locnho/chem-feeder-mqtt/test-images/000b.jpg

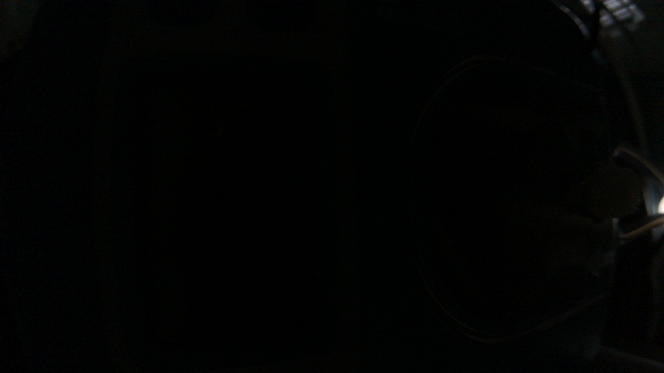
test-images/000b.jpg
