locnho/chem-feeder-mqtt/test-images/000c.jpg

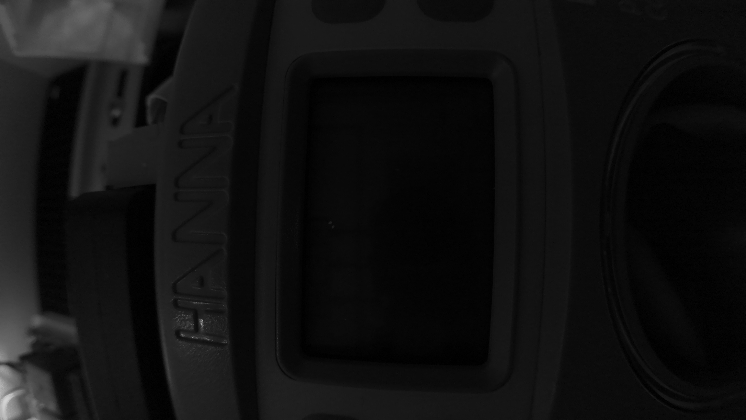
test-images/000c.jpg
