locnho/chem-feeder-mqtt/test-images/680.jpg

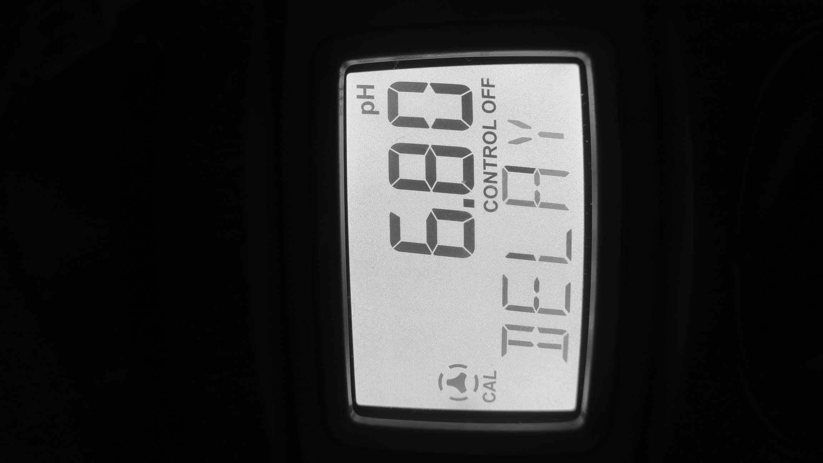
test-images/680.jpg
