locnho/chem-feeder-mqtt/test-images/729.jpg

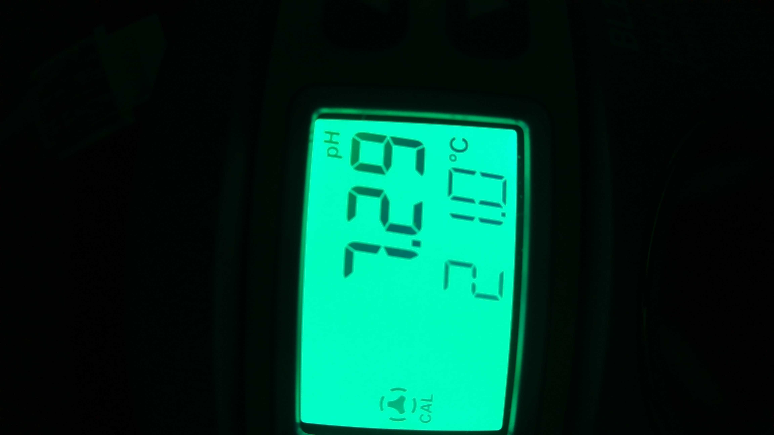
test-images/729.jpg
