locnho/chem-feeder-mqtt/test-images/731.jpg

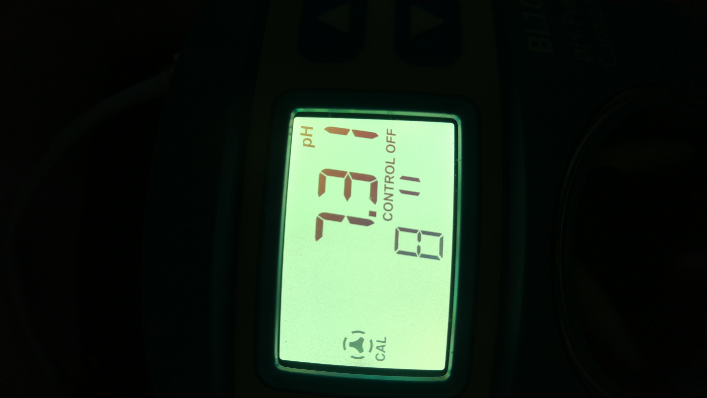
test-images/731.jpg
