locnho/chem-feeder-mqtt/test-images/733.jpg

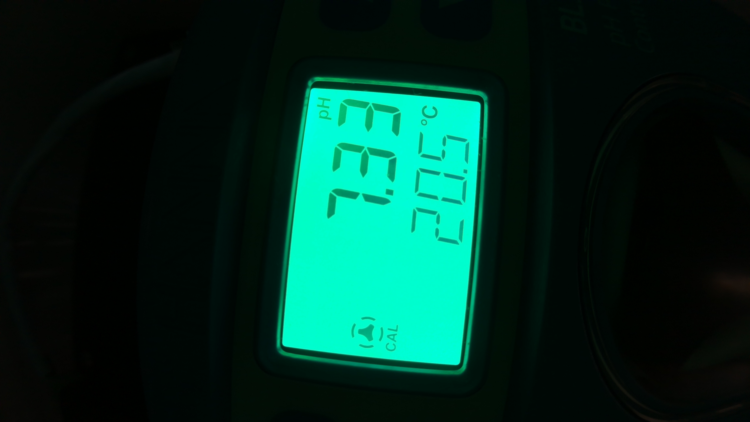
test-images/733.jpg
