locnho/chem-feeder-mqtt/test-images/735b.jpg

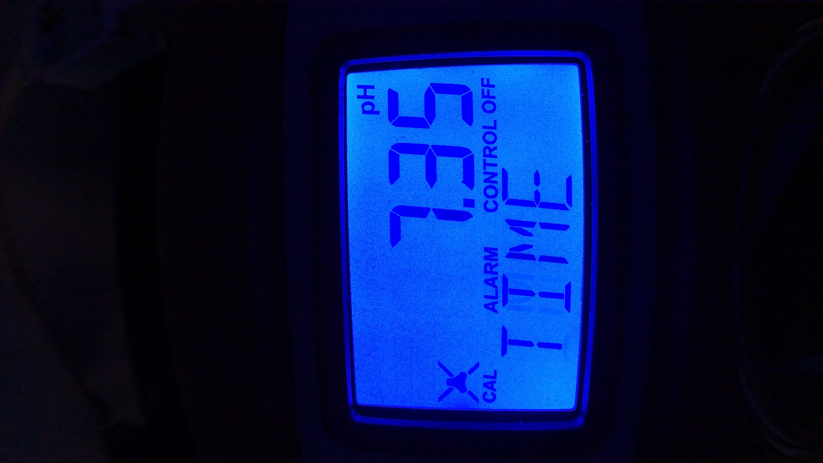
test-images/735b.jpg
