locnho/chem-feeder-mqtt/test-images/740.jpg

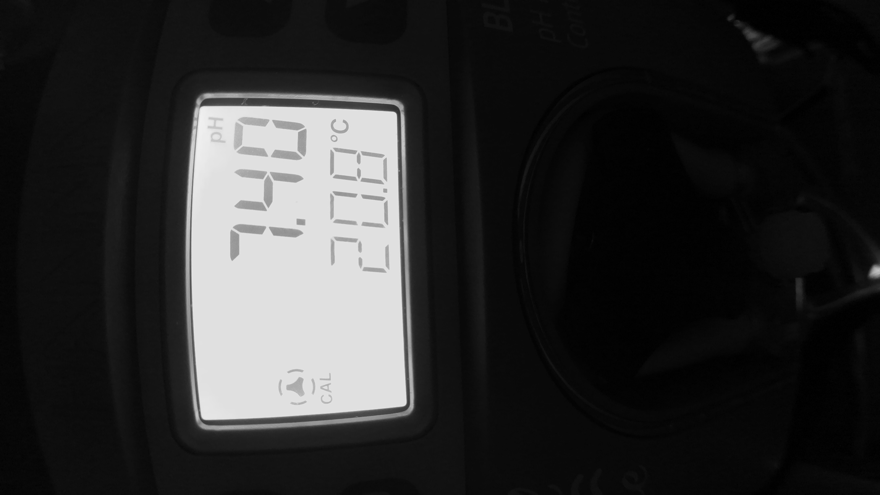
test-images/740.jpg
