locnho/chem-feeder-mqtt/test-images/742a.jpg

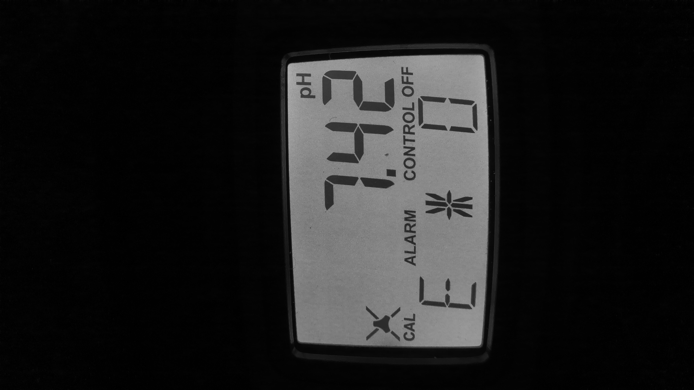
test-images/742a.jpg
