locnho/chem-feeder-mqtt/test-images/742ab.jpg

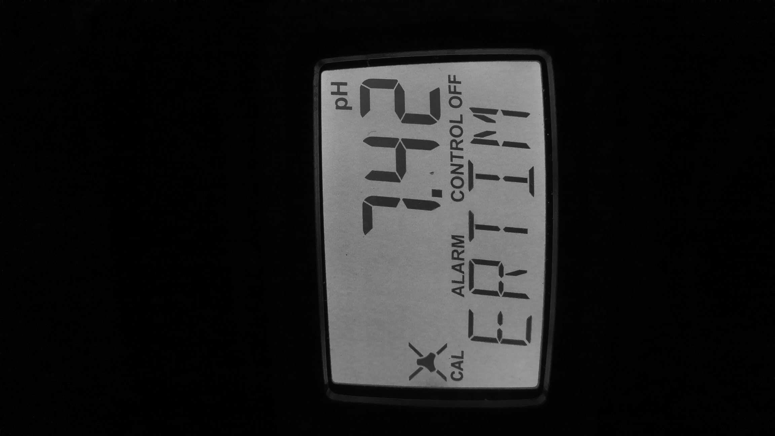
test-images/742ab.jpg
