locnho/chem-feeder-mqtt/test-images/760.jpg

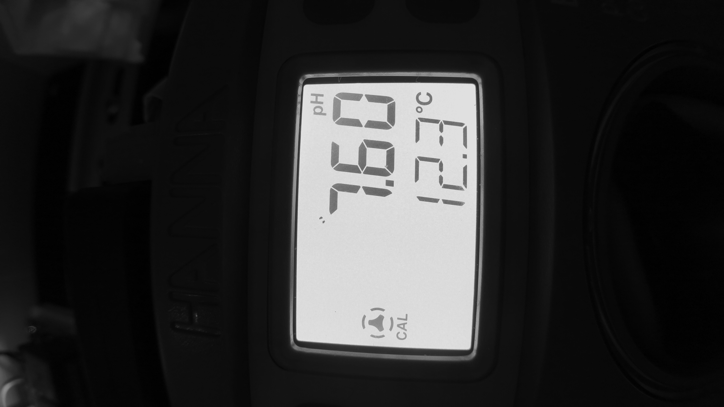
test-images/760.jpg
